kbranch/snowflake_keyboard/stls/keycaps/legends/Keycap - Legend - 0.stl

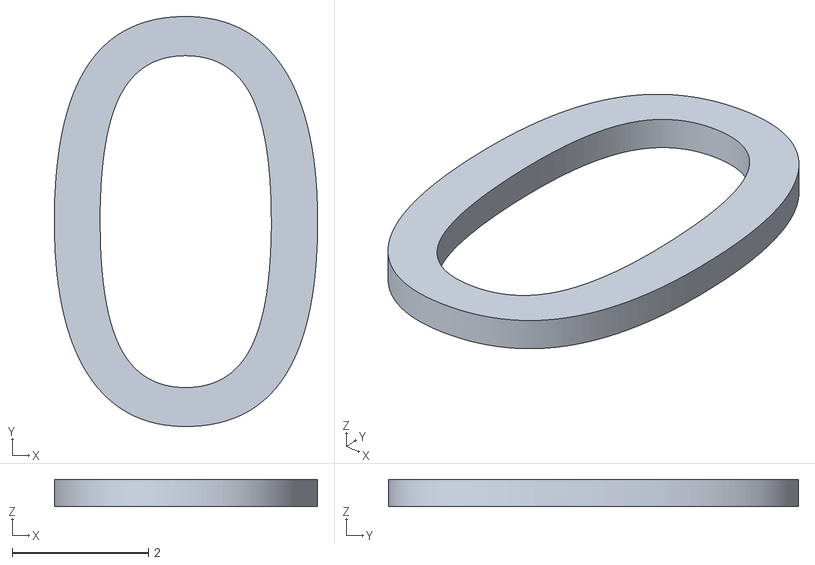
[picture p12: CAD file, 2021-06-19]
stls/keycaps/legends/Keycap - Legend - 0.stl
3.87 x 6.02 x 0.4
