kbranch/snowflake_keyboard/stls/keycaps/legends/Keycap - Legend - X.stl

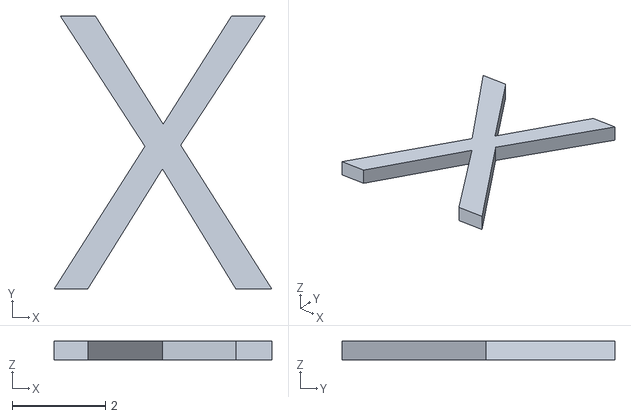
[picture p13: CAD file, 2021-06-19]
stls/keycaps/legends/Keycap - Legend - X.stl
4.67 x 5.85 x 0.4
