kbranch/snowflake_keyboard/stls/keycaps/legends/Snowflake layers.3mf

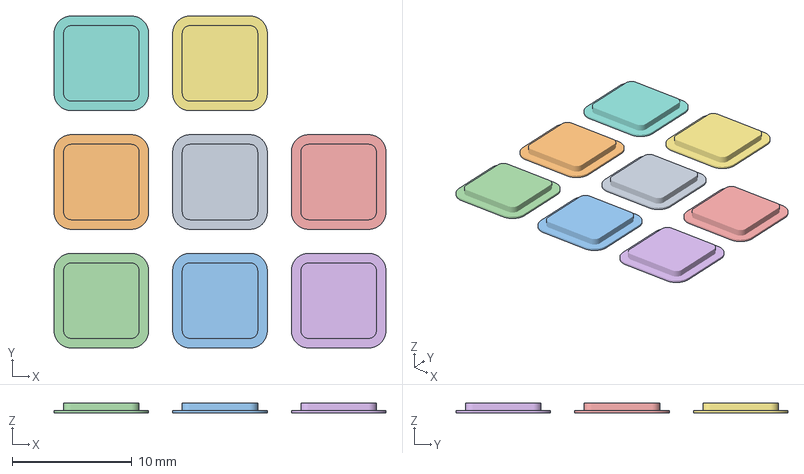
[picture p14: CAD file, 2021-06-19]
stls/keycaps/legends/Snowflake layers.3mf
27.7 x 27.7 x 0.8 mm
Keycap - Legend - L4(1).stl
Keycap - Legend - L2(1).stl
Keycap - Legend - L3(1).stl
Keycap - Legend Block - L1(1).stl
