kbranch/snowflake_keyboard/stls/Snowflake - Left Base.stl

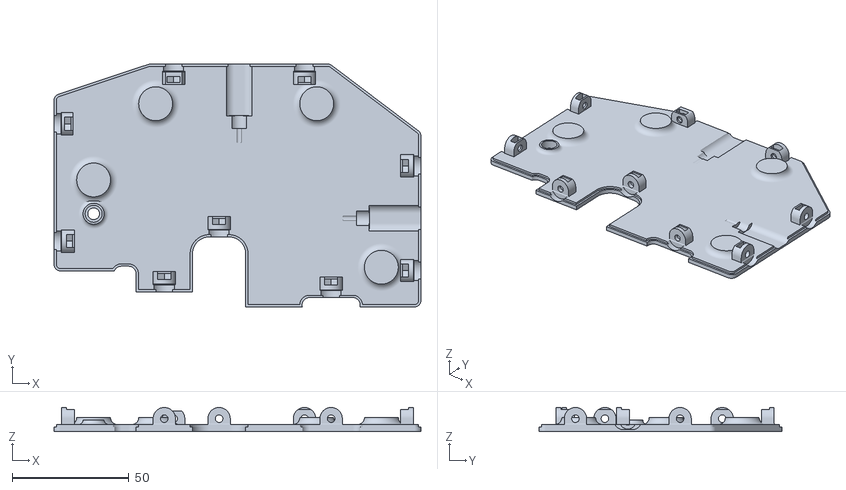
[picture p15: CAD file, 2021-06-19]
stls/Snowflake - Left Base.stl
157.4 x 104.1 x 10.3
