kbranch/snowflake_keyboard/stls/keycaps/legends/Keycap - Legend - 6.stl

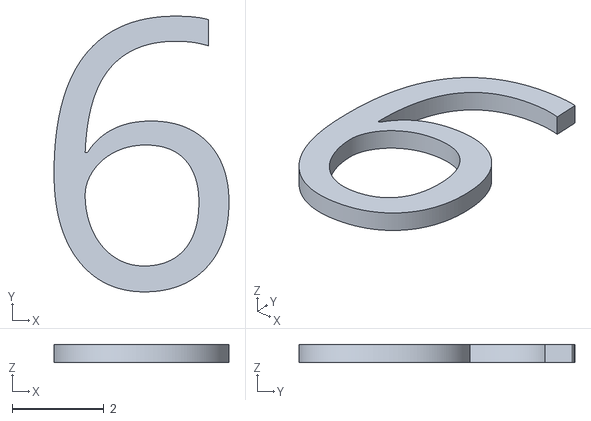
[picture p16: CAD file, 2021-06-19]
stls/keycaps/legends/Keycap - Legend - 6.stl
3.82 x 6.01 x 0.4
