kbranch/snowflake_keyboard/stls/Snowflake - Right Palm Rest.stl

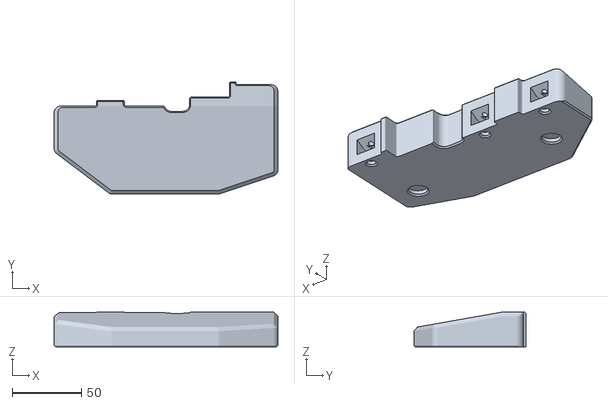
[picture p17: CAD file, 2021-06-19]
stls/Snowflake - Right Palm Rest.stl
161.8 x 81.0 x 25.1
