kbranch/snowflake_keyboard/stls/keycaps/legends/Keycap - Legend - Y.stl

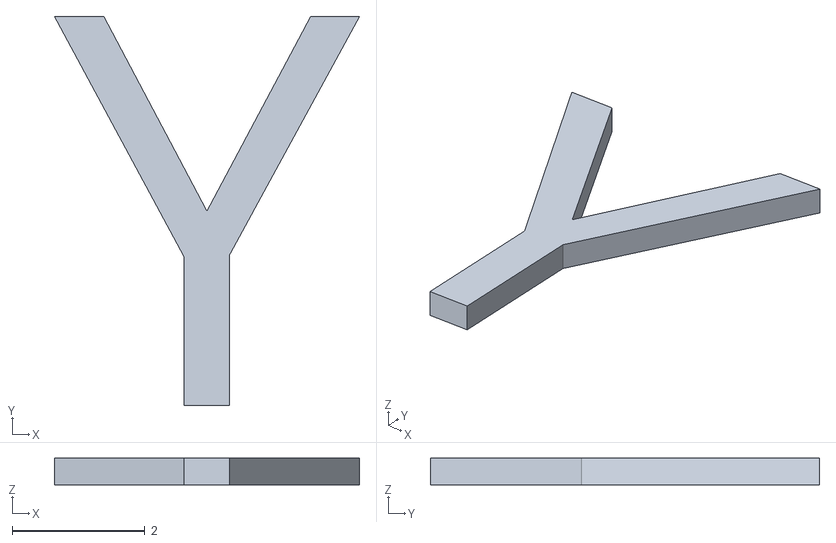
[picture p18: CAD file, 2021-06-19]
stls/keycaps/legends/Keycap - Legend - Y.stl
4.59 x 5.85 x 0.4
