kbranch/snowflake_keyboard/stls/Snowflake - Left Plate.stl

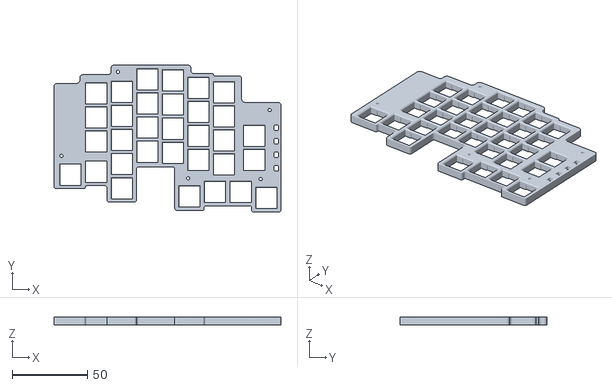
[picture p19: CAD file, 2021-06-19]
stls/Snowflake - Left Plate.stl
150.8 x 97.5 x 5.00
