kbranch/snowflake_keyboard/stls/keycaps/legends/Keycap - Legend - T.stl

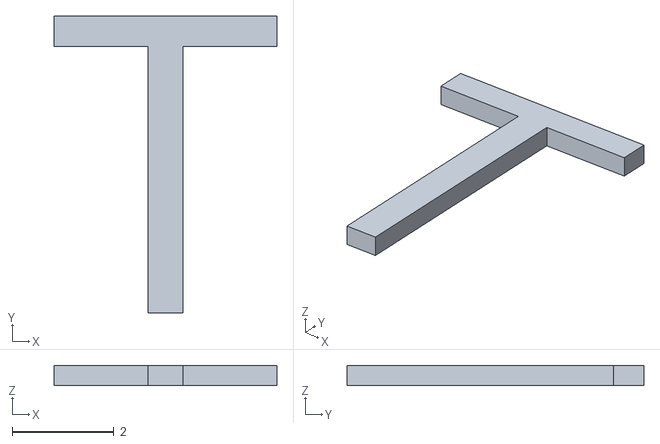
[picture p20: CAD file, 2021-06-19]
stls/keycaps/legends/Keycap - Legend - T.stl
4.39 x 5.85 x 0.4
