kbranch/snowflake_keyboard/stls/keycaps/legends/Keycap - Legend - C.stl

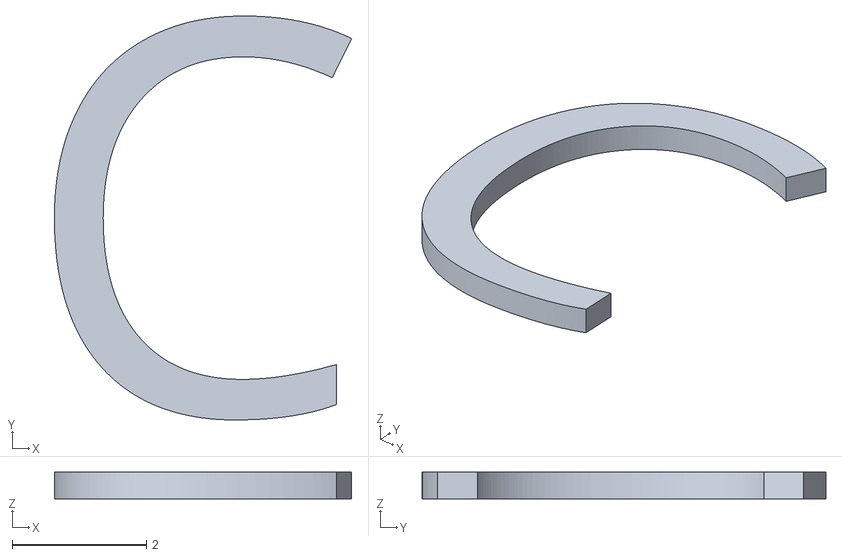
[picture p21: CAD file, 2021-06-19]
stls/keycaps/legends/Keycap - Legend - C.stl
4.43 x 6.01 x 0.4
