kbranch/snowflake_keyboard/stls/keycaps/legends/Keycap - Legend - H.stl

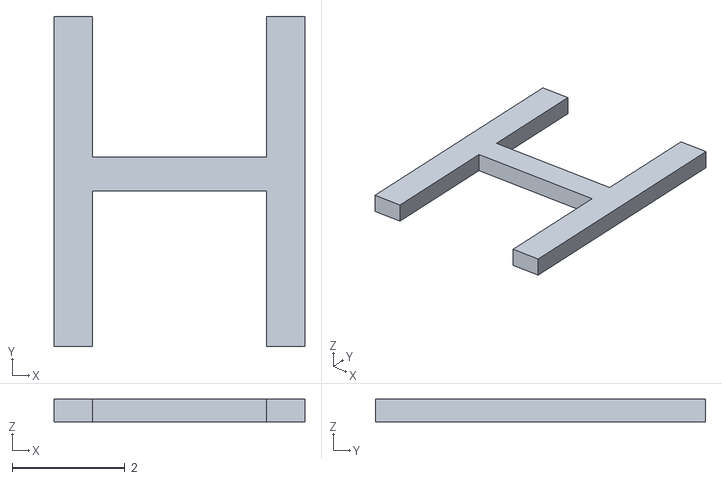
[picture p22: CAD file, 2021-06-19]
stls/keycaps/legends/Keycap - Legend - H.stl
4.44 x 5.85 x 0.4
