kbranch/snowflake_keyboard/stls/keycaps/legends/Keycap - Legend - W.stl

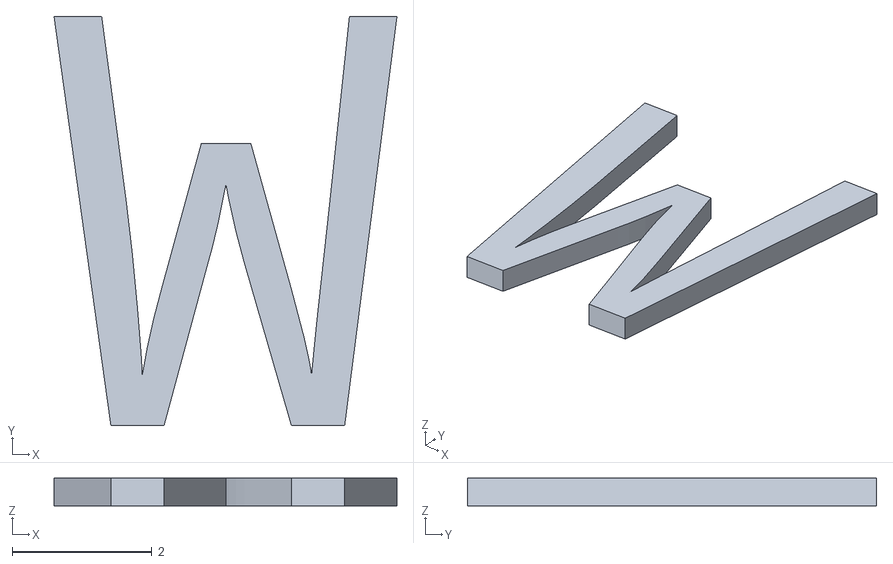
[picture p23: CAD file, 2021-06-19]
stls/keycaps/legends/Keycap - Legend - W.stl
4.90 x 5.85 x 0.4
