kbranch/snowflake_keyboard/stls/keycaps/legends/Keycap - Legend - I.stl

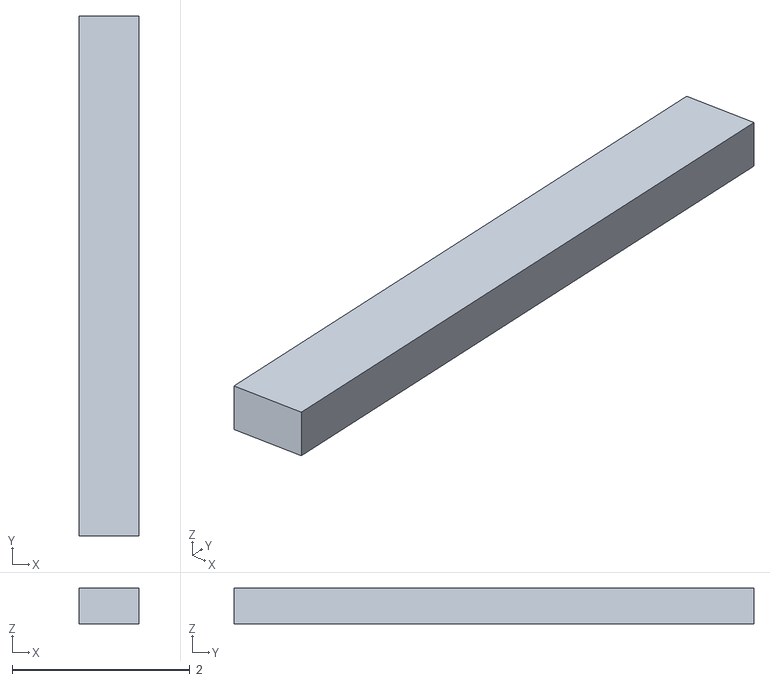
[picture p24: CAD file, 2021-06-19]
stls/keycaps/legends/Keycap - Legend - I.stl
0.68 x 5.85 x 0.4
