kbranch/snowflake_keyboard/stls/keycaps/legends/Keycap - Legend - S.stl

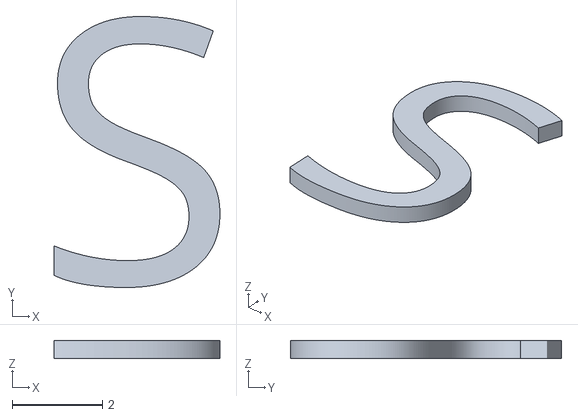
[picture p25: CAD file, 2021-06-19]
stls/keycaps/legends/Keycap - Legend - S.stl
3.68 x 6.01 x 0.4
