kbranch/snowflake_keyboard/stls/keycaps/legends/Keycap - Legend - L2.stl

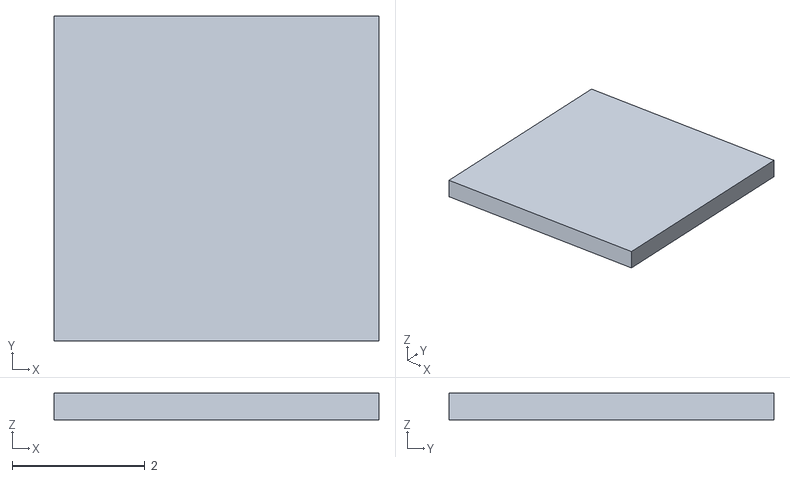
[picture p26: CAD file, 2021-06-19]
stls/keycaps/legends/Keycap - Legend - L2.stl
4.90 x 4.90 x 0.4
