kbranch/snowflake_keyboard/stls/keycaps/legends/Keycap - Legend - F.stl

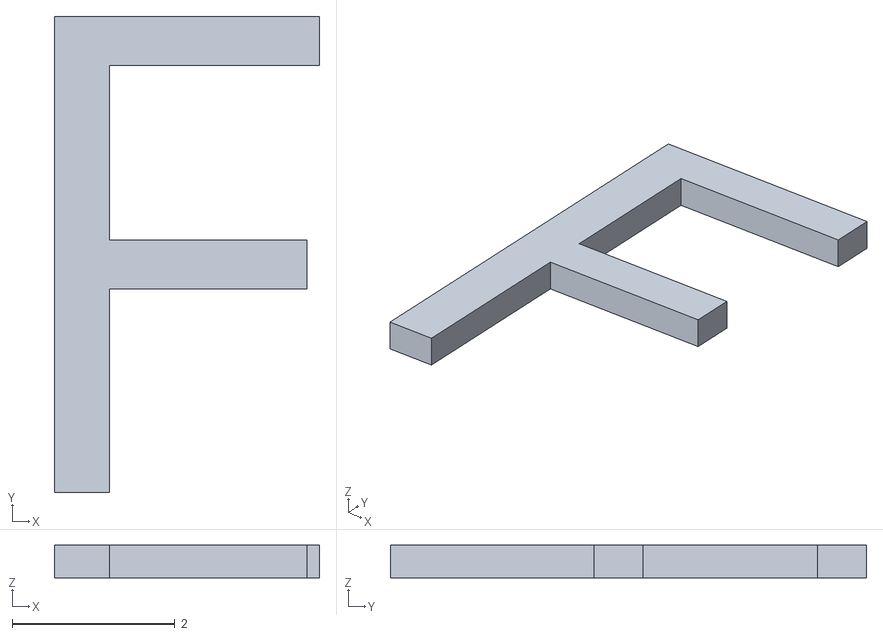
[picture p27: CAD file, 2021-06-19]
stls/keycaps/legends/Keycap - Legend - F.stl
3.26 x 5.85 x 0.4
