kbranch/snowflake_keyboard/stls/keycaps/legends/Keycap - Legend - M.stl

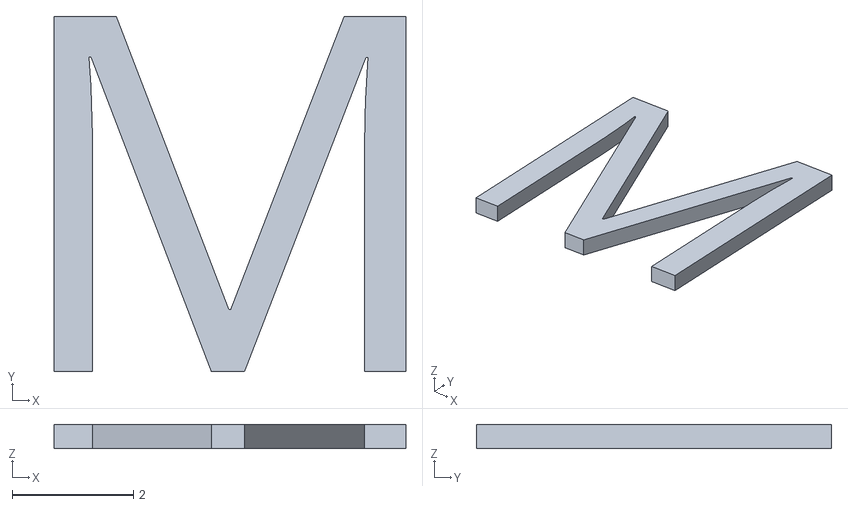
[picture p28: CAD file, 2021-06-19]
stls/keycaps/legends/Keycap - Legend - M.stl
5.79 x 5.85 x 0.4
