kbranch/snowflake_keyboard/stls/keycaps/legends/Keycap - Legend - Tab.stl

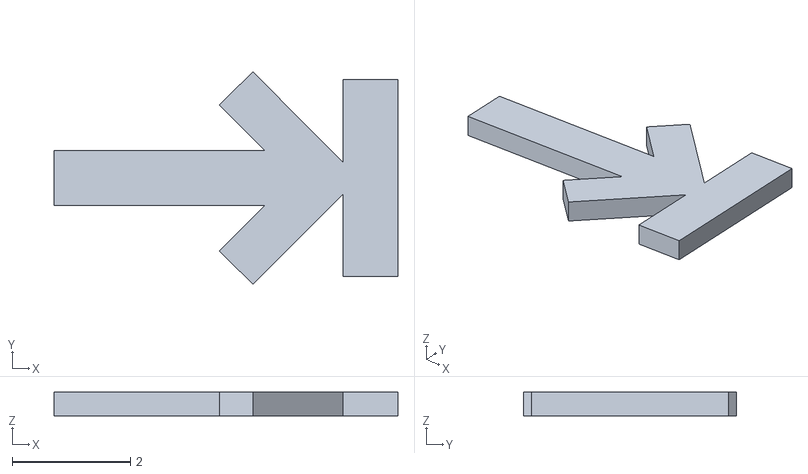
[picture p29: CAD file, 2021-06-19]
stls/keycaps/legends/Keycap - Legend - Tab.stl
5.81 x 3.59 x 0.4
