kbranch/snowflake_keyboard/stls/keycaps/legends/Keycap - Legend - O.stl

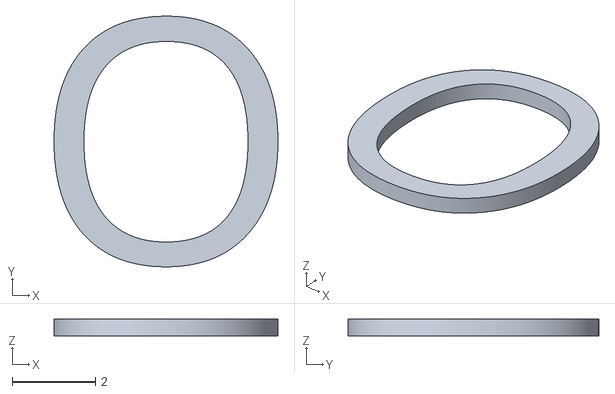
[picture p30: CAD file, 2021-06-19]
stls/keycaps/legends/Keycap - Legend - O.stl
5.38 x 6.02 x 0.4
