kbranch/snowflake_keyboard/stls/keycaps/legends/Keycap - Legend - B.stl

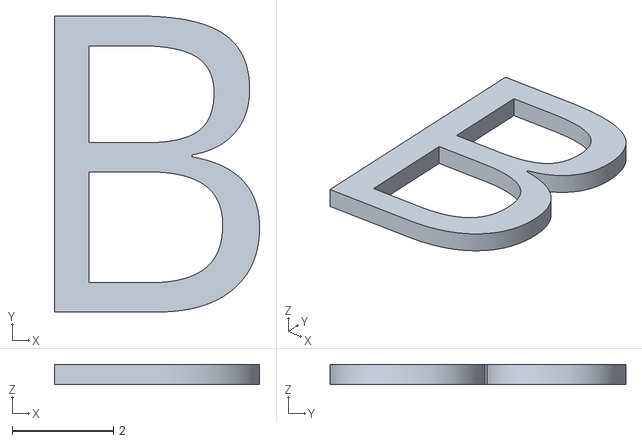
[picture p31: CAD file, 2021-06-19]
stls/keycaps/legends/Keycap - Legend - B.stl
4.05 x 5.85 x 0.4
