kbranch/snowflake_keyboard/stls/keycaps/legends/Keycap - Legend - 7.stl

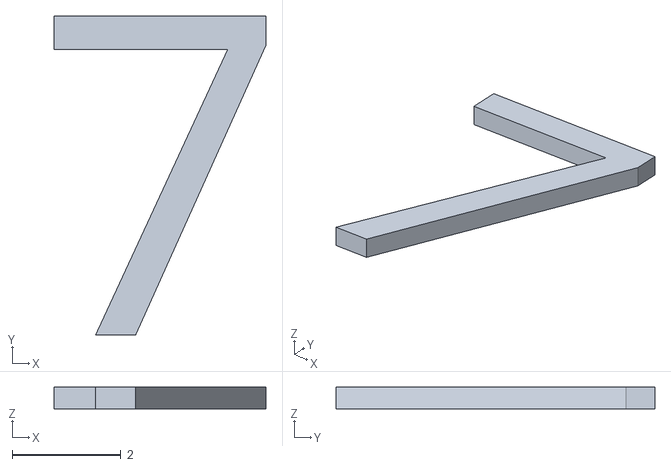
[picture p32: CAD file, 2021-06-19]
stls/keycaps/legends/Keycap - Legend - 7.stl
3.89 x 5.85 x 0.4
