kbranch/snowflake_keyboard/stls/keycaps/legends/Snoflake Alphas.3mf

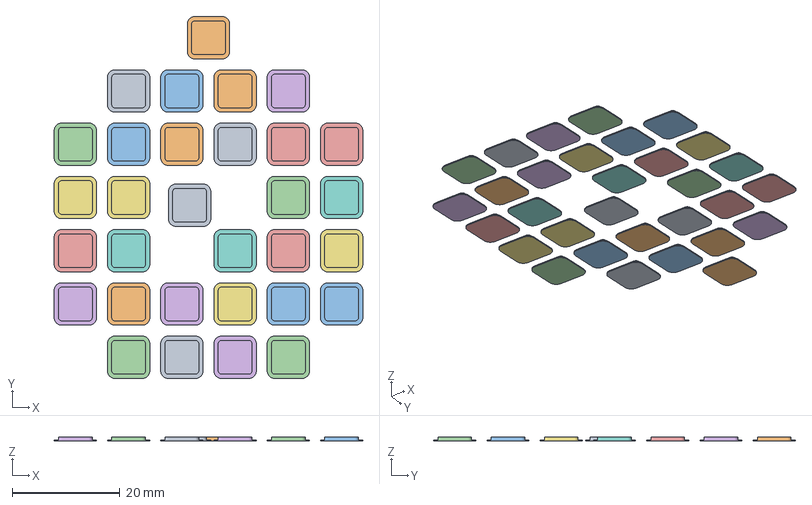
[picture p33: CAD file, 2021-06-19]
stls/keycaps/legends/Snoflake Alphas.3mf
57.4 x 67.3 x 0.802 mm
Keycap - Legend - A(4).stl
Keycap - Legend - B(2).stl
Keycap - Legend - C(2).stl
Keycap - Legend - D(3).stl
Keycap - Legend - E(2).stl
Keycap - Legend - F(3).stl
Keycap - Legend - G(2).stl
Keycap - Legend - H(2).stl
Keycap - Legend - I(2).stl
Keycap - Legend - J(2).stl
Keycap - Legend - K(2).stl
Keycap - Legend - L(2).stl
Keycap - Legend - N(2).stl
Keycap - Legend - M(2).stl
Keycap - Legend - O(2).stl
Keycap - Legend - P(2).stl
Keycap - Legend - Q(4).stl
Keycap - Legend - R(2).stl
Keycap - Legend - S(3).stl
Keycap - Legend - T(2).stl
Keycap - Legend - U(2).stl
Keycap - Legend - V(2).stl
Keycap - Legend - W(2).stl
Keycap - Legend - X(2).stl
Keycap - Legend - Y(2).stl
Keycap - Legend - Z(2).stl
Keycap - Legend - ,(2).stl
Keycap - Legend - .(2).stl
Keycap - Legend - ;-.stl
Keycap - Legend - `~(1).stl
Keycap - Legend - --.stl
