kbranch/snowflake_keyboard/stls/keycaps/legends/Keycap - Legend - 3.stl

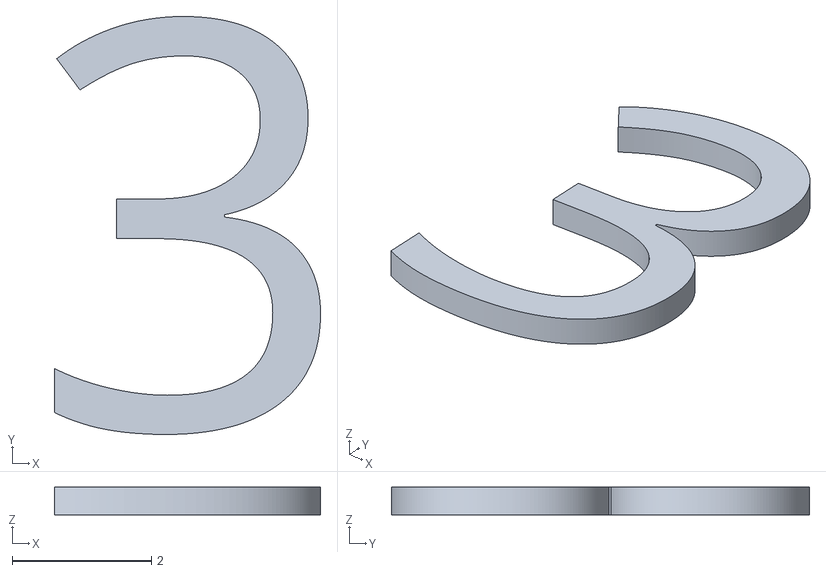
[picture p34: CAD file, 2021-06-19]
stls/keycaps/legends/Keycap - Legend - 3.stl
3.83 x 6.01 x 0.4
