kbranch/snowflake_keyboard/stls/keycaps/legends/Keycap - Legend - L4.stl

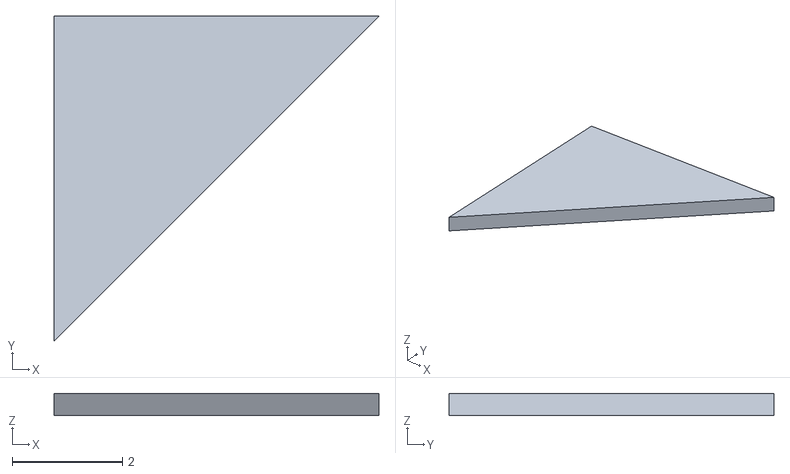
[picture p35: CAD file, 2021-06-19]
stls/keycaps/legends/Keycap - Legend - L4.stl
5.90 x 5.90 x 0.4
