kbranch/snowflake_keyboard/stls/keycaps/legends/Keycap - Legend - K.stl

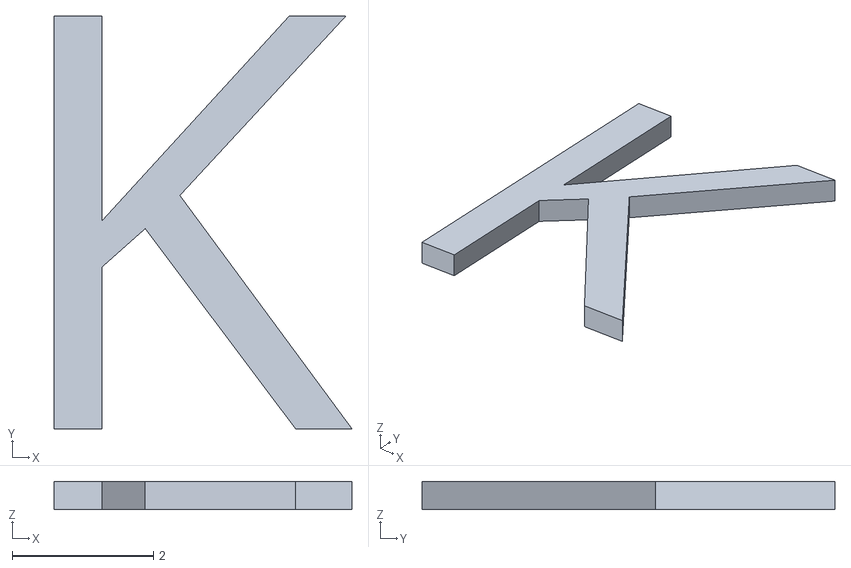
[picture p36: CAD file, 2021-06-19]
stls/keycaps/legends/Keycap - Legend - K.stl
4.23 x 5.85 x 0.4
