kbranch/snowflake_keyboard/stls/keycaps/legends/Keycap - Legend - Shift.stl

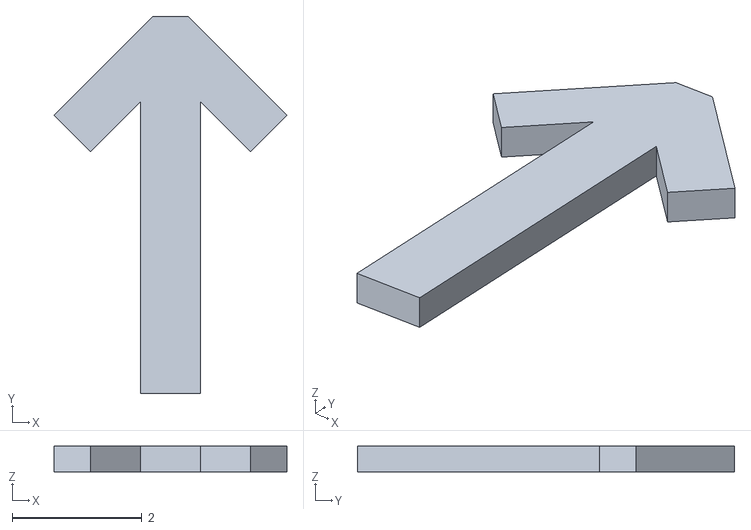
[picture p37: CAD file, 2021-06-19]
stls/keycaps/legends/Keycap - Legend - Shift.stl
3.59 x 5.82 x 0.4
