kbranch/snowflake_keyboard/stls/keycaps/legends/Keycap - Legend - Alt.stl

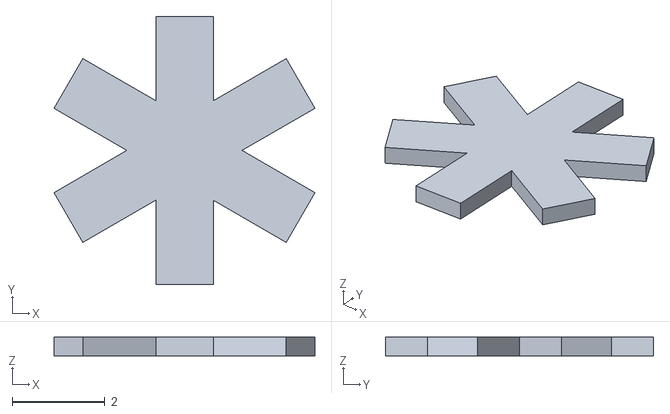
[picture p38: CAD file, 2021-06-19]
stls/keycaps/legends/Keycap - Legend - Alt.stl
5.63 x 5.79 x 0.4
