kbranch/snowflake_keyboard/stls/keycaps/legends/Keycap - Legend - U.stl

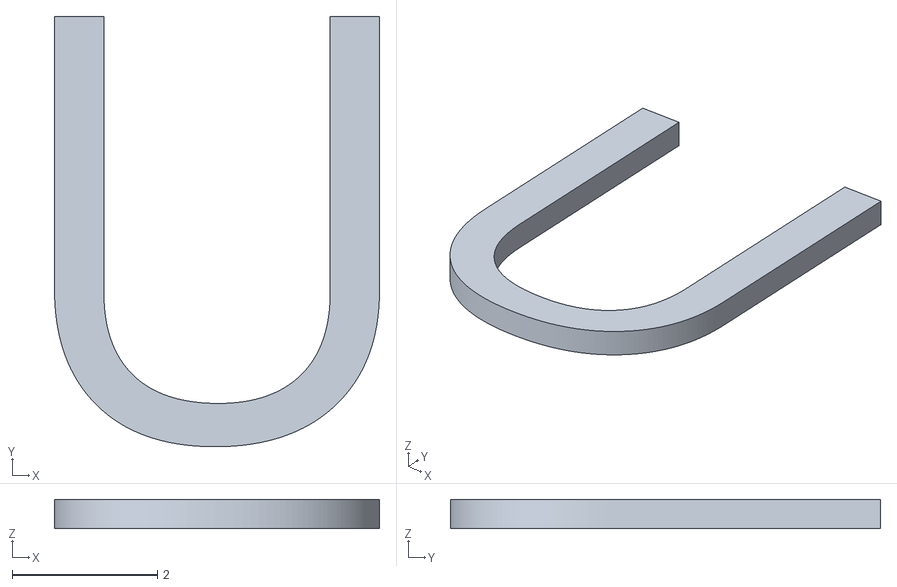
[picture p39: CAD file, 2021-06-19]
stls/keycaps/legends/Keycap - Legend - U.stl
4.48 x 5.93 x 0.4
