kbranch/snowflake_keyboard/stls/keycaps/legends/Keycap - Legend - P.stl

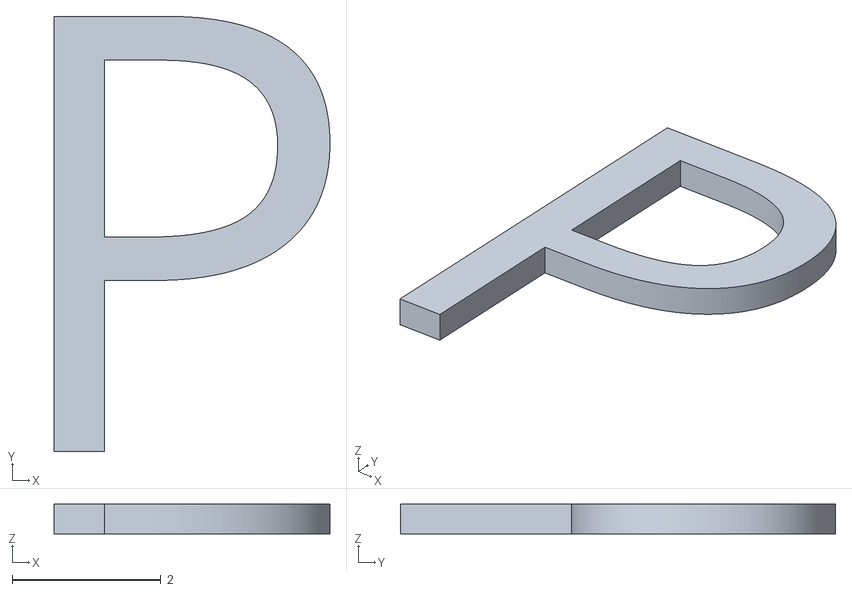
[picture p40: CAD file, 2021-06-19]
stls/keycaps/legends/Keycap - Legend - P.stl
3.71 x 5.85 x 0.4
