kbranch/snowflake_keyboard/stls/keycaps/legends/Keycap - Legend - Return.stl

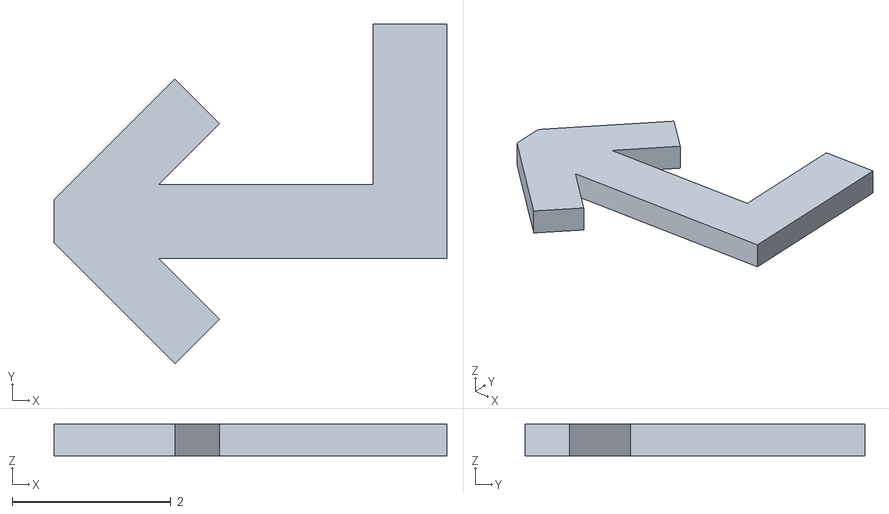
[picture p41: CAD file, 2021-06-19]
stls/keycaps/legends/Keycap - Legend - Return.stl
4.96 x 4.28 x 0.4
