kbranch/snowflake_keyboard/stls/keycaps/legends/Keycap - Legend - V.stl

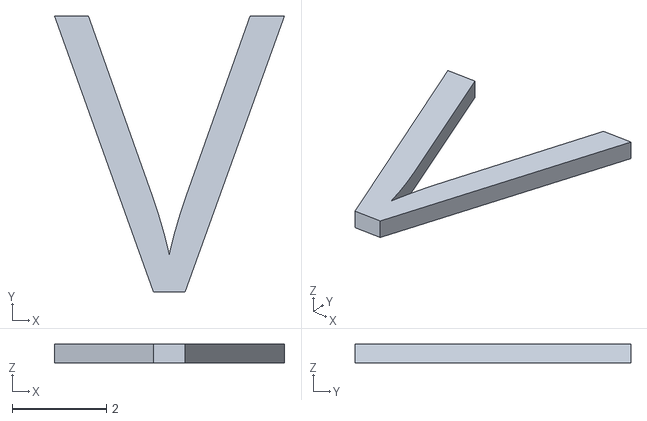
[picture p42: CAD file, 2021-06-19]
stls/keycaps/legends/Keycap - Legend - V.stl
4.88 x 5.85 x 0.4
