kbranch/snowflake_keyboard/stls/keycaps/legends/Keycap - Legend Block - N.stl

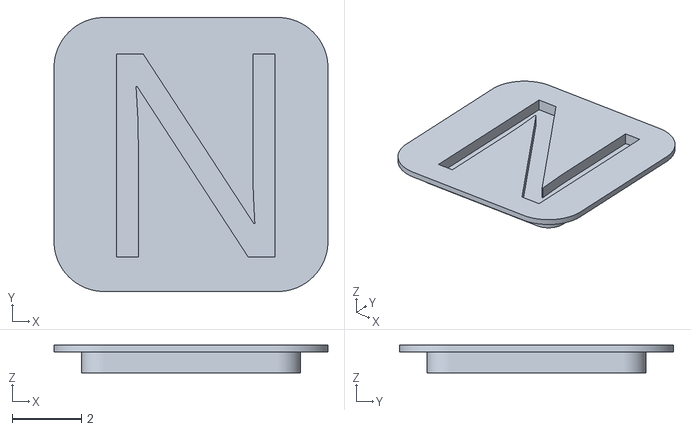
[picture p43: CAD file, 2021-06-19]
stls/keycaps/legends/Keycap - Legend Block - N.stl
7.90 x 7.90 x 0.8
