kbranch/snowflake_keyboard/stls/keycaps/legends/Keycap - Legend - 4.stl

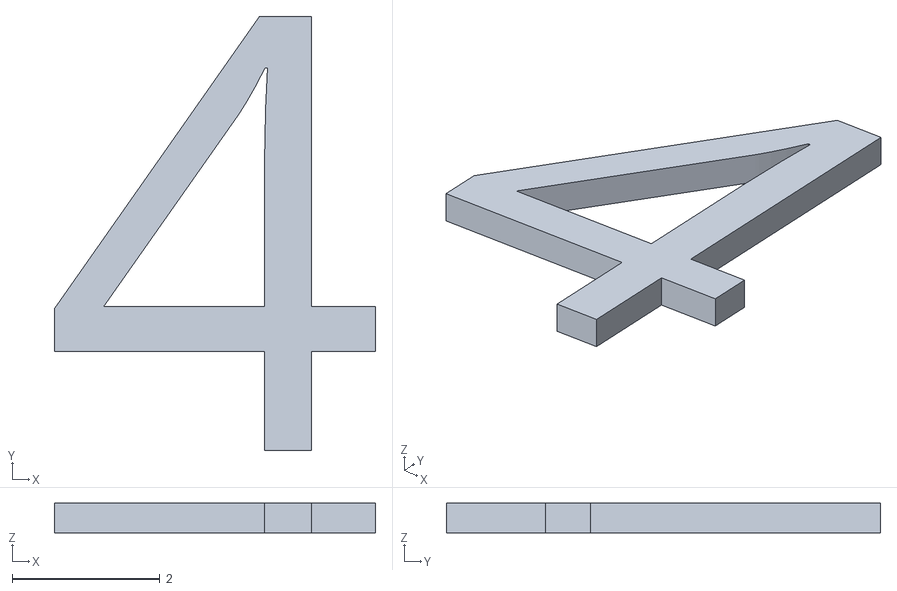
[picture p44: CAD file, 2021-06-19]
stls/keycaps/legends/Keycap - Legend - 4.stl
4.35 x 5.88 x 0.4
