kbranch/snowflake_keyboard/stls/keycaps/legends/Keycap - Legend - L.stl

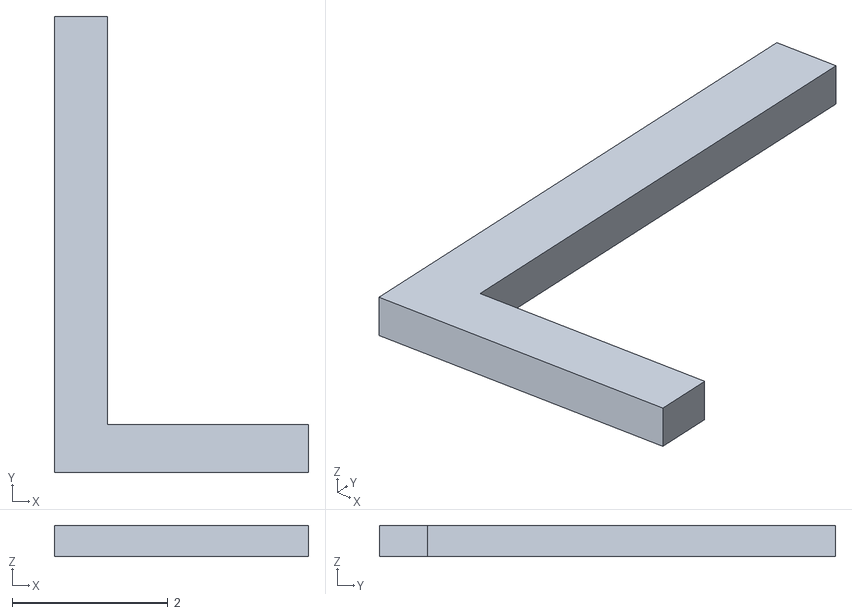
[picture p45: CAD file, 2021-06-19]
stls/keycaps/legends/Keycap - Legend - L.stl
3.26 x 5.85 x 0.4
