kbranch/snowflake_keyboard/stls/keycaps/legends/Keycap - Legend Block - A.stl

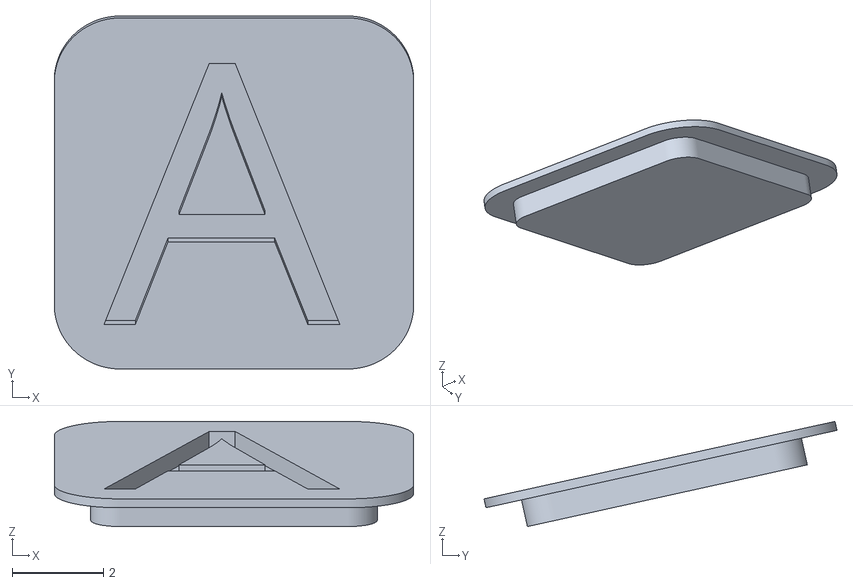
[picture p47: CAD file, 2021-06-19]
stls/keycaps/legends/Keycap - Legend Block - A.stl
7.90 x 7.76 x 2.31
