kbranch/snowflake_keyboard/stls/keycaps/legends/Keycap - Legend - A.stl

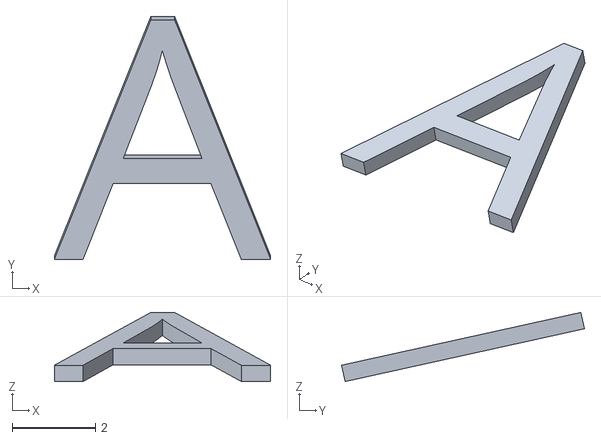
[picture p48: CAD file, 2021-06-19]
stls/keycaps/legends/Keycap - Legend - A.stl
5.19 x 5.82 x 1.66
