kbranch/snowflake_keyboard/stls/keycaps/legends/Keycap - Legend - Z.stl

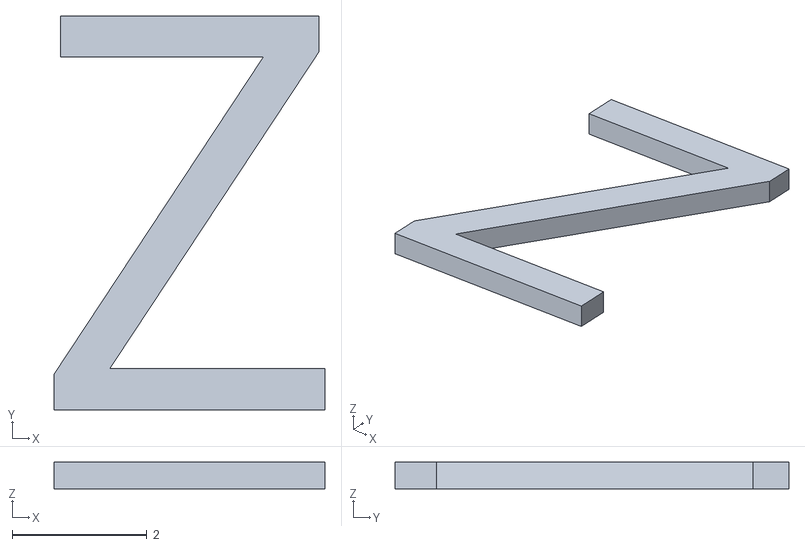
[picture p49: CAD file, 2021-06-19]
stls/keycaps/legends/Keycap - Legend - Z.stl
4.02 x 5.85 x 0.4
