kbranch/snowflake_keyboard/stls/keycaps/legends/Snowflake white.3mf

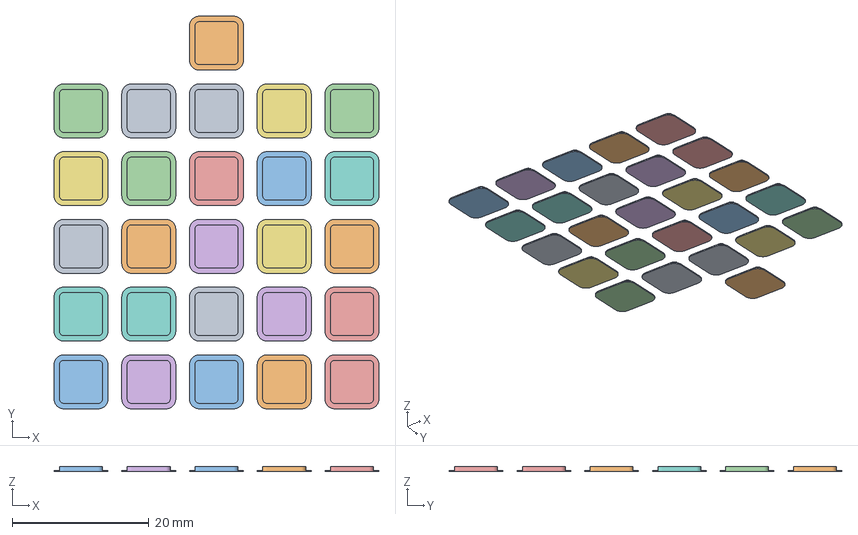
[picture p50: CAD file, 2021-06-19]
stls/keycaps/legends/Snowflake white.3mf
47.5 x 57.4 x 0.8 mm
Keycap - Legend - `~(1).stl
Keycap - Legend - 1(2).stl
Keycap - Legend - 2(2).stl
Keycap - Legend - 3(2).stl
Keycap - Legend - 4(2).stl
Keycap - Legend - 5(2).stl
Keycap - Legend - 6(2).stl
Keycap - Legend - 7(2).stl
Keycap - Legend - 8(2).stl
Keycap - Legend - 9(2).stl
Keycap - Legend - 0(2).stl
Keycap - Legend - --(1).stl
Keycap - Legend - '-(3).stl
Keycap - Legend - ^(1).stl
Keycap - Legend - Shift(1).stl
Keycap - Legend - Tab(1).stl
Keycap - Legend - Alt(1).stl
Keycap.stl
Keycap - Legend - Space(1).stl
Keycap - Legend - Backspace(1).stl
Keycap - Legend - Return(1).stl
