kbranch/snowflake_keyboard/stls/keycaps/legends/Keycap - Legend - '-.stl

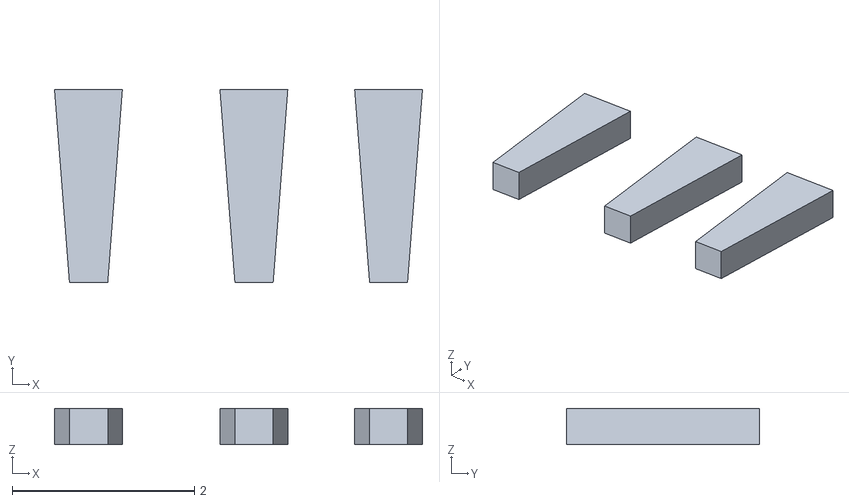
[picture p51: CAD file, 2021-06-19]
stls/keycaps/legends/Keycap - Legend - '-.stl
4.03 x 2.11 x 0.4
