kbranch/snowflake_keyboard/stls/keycaps/legends/Keycap - Legend - Q.stl

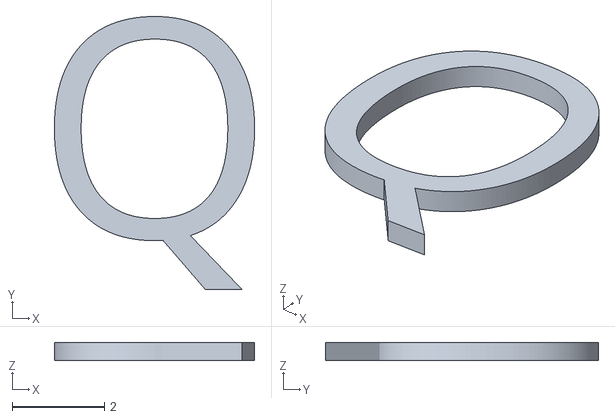
[picture p52: CAD file, 2021-06-19]
stls/keycaps/legends/Keycap - Legend - Q.stl
4.33 x 5.91 x 0.4
