kbranch/snowflake_keyboard/stls/keycaps/legends/Keycap - Legend - R.stl

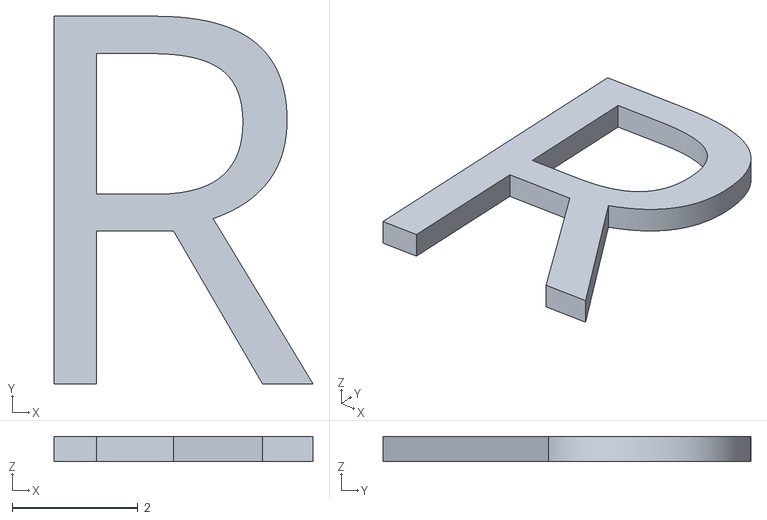
[picture p53: CAD file, 2021-06-19]
stls/keycaps/legends/Keycap - Legend - R.stl
4.12 x 5.85 x 0.4
