kbranch/snowflake_keyboard/stls/keycaps/legends/Keycap - Legend - Space.stl

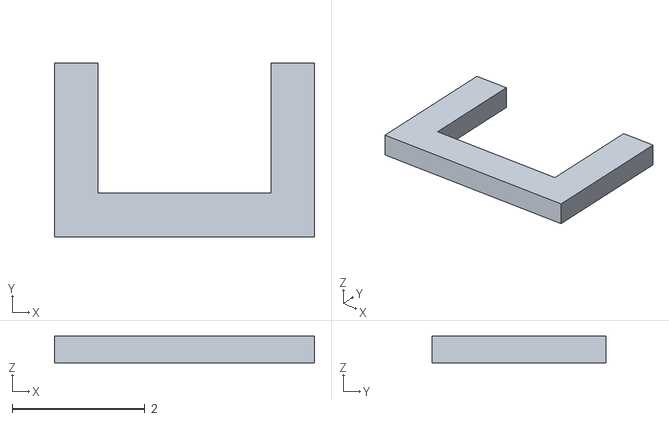
[picture p54: CAD file, 2021-06-19]
stls/keycaps/legends/Keycap - Legend - Space.stl
3.91 x 2.61 x 0.4
