kbranch/snowflake_keyboard/stls/keycaps/legends/Keycap - Legend - L1.stl

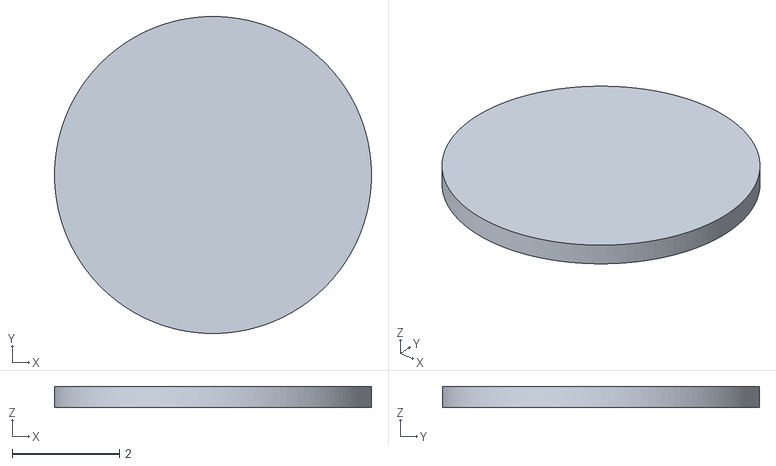
[picture p55: CAD file, 2021-06-19]
stls/keycaps/legends/Keycap - Legend - L1.stl
5.90 x 5.90 x 0.4
