kbranch/snowflake_keyboard/stls/keycaps/legends/Keycap - Legend - L3.stl

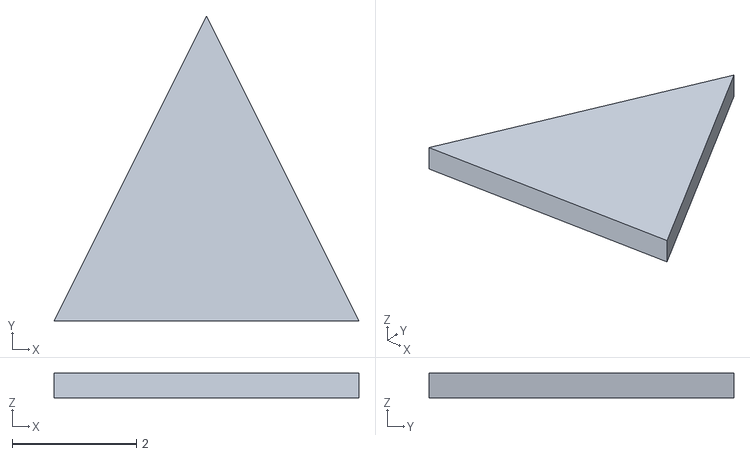
[picture p56: CAD file, 2021-06-19]
stls/keycaps/legends/Keycap - Legend - L3.stl
4.90 x 4.90 x 0.4
