kbranch/snowflake_keyboard/stls/keycaps/legends/Keycap - Legend - D.stl

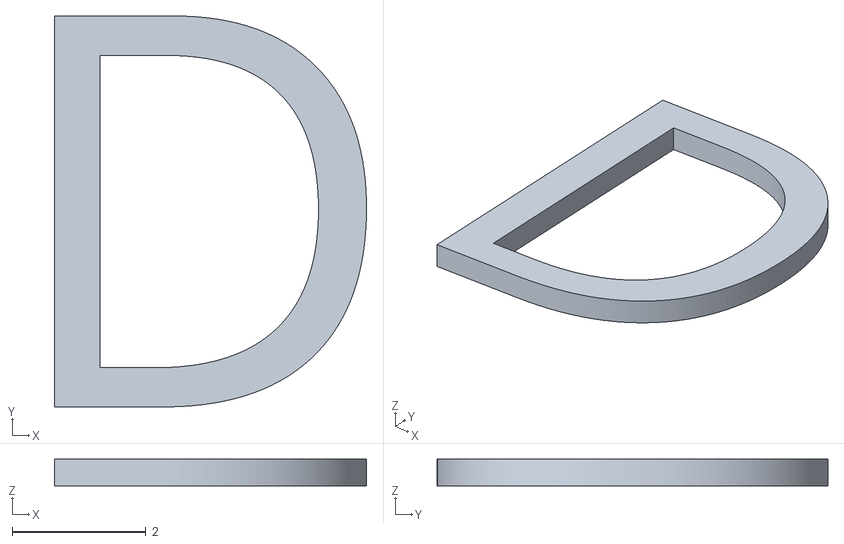
[picture p57: CAD file, 2021-06-19]
stls/keycaps/legends/Keycap - Legend - D.stl
4.67 x 5.85 x 0.4
