kbranch/snowflake_keyboard/stls/keycaps/legends/Keycap - Legend - 8.stl

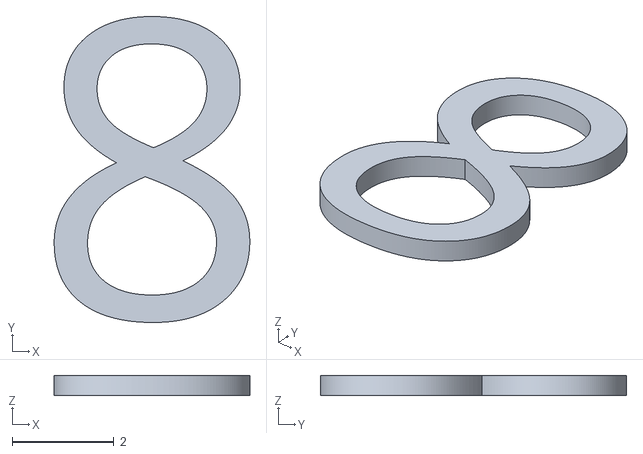
[picture p58: CAD file, 2021-06-19]
stls/keycaps/legends/Keycap - Legend - 8.stl
3.84 x 6.01 x 0.4
