kbranch/snowflake_keyboard/stls/keycaps/legends/Keycap - Legend - J.stl

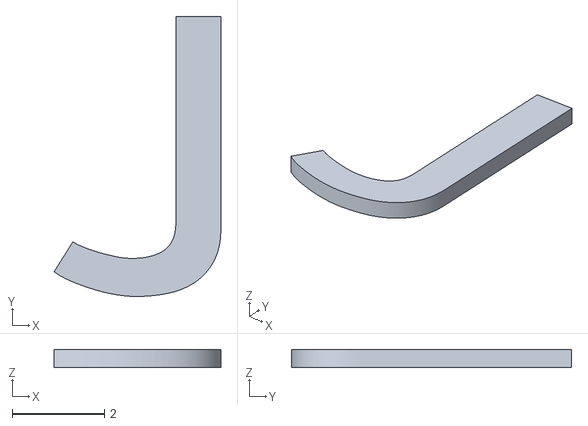
[picture p59: CAD file, 2021-06-19]
stls/keycaps/legends/Keycap - Legend - J.stl
3.61 x 6.06 x 0.4
