kbranch/snowflake_keyboard/stls/keycaps/legends/Keycap - Legend - 2.stl

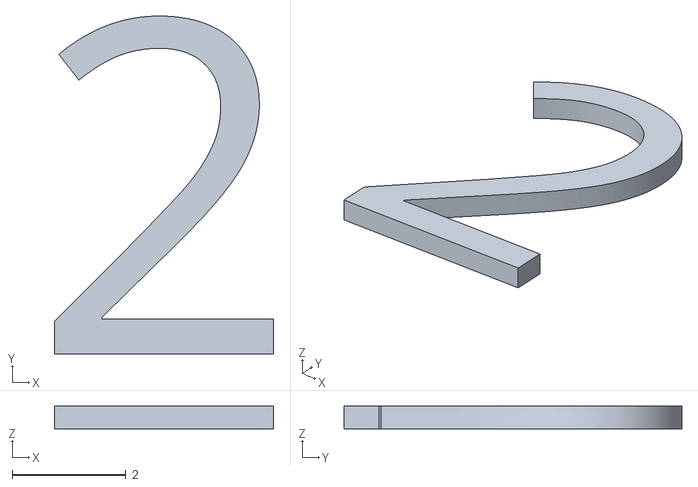
[picture p60: CAD file, 2021-06-19]
stls/keycaps/legends/Keycap - Legend - 2.stl
3.84 x 5.93 x 0.4
