kbranch/snowflake_keyboard/stls/keycaps/legends/Keycap - Legend - N.stl

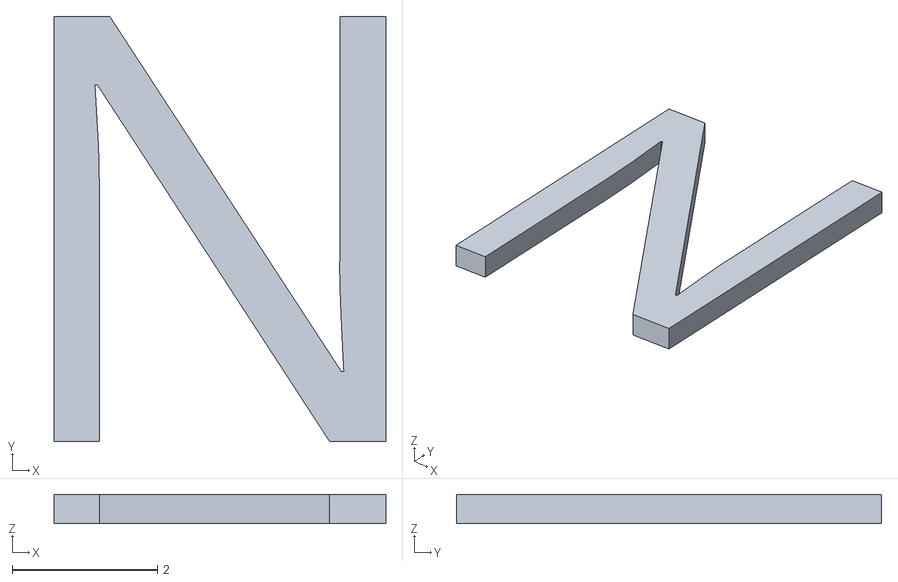
[picture p61: CAD file, 2021-06-19]
stls/keycaps/legends/Keycap - Legend - N.stl
4.57 x 5.85 x 0.4
